Resaj/pumatron-v1/images/V1.2/DSCF2929.jpg

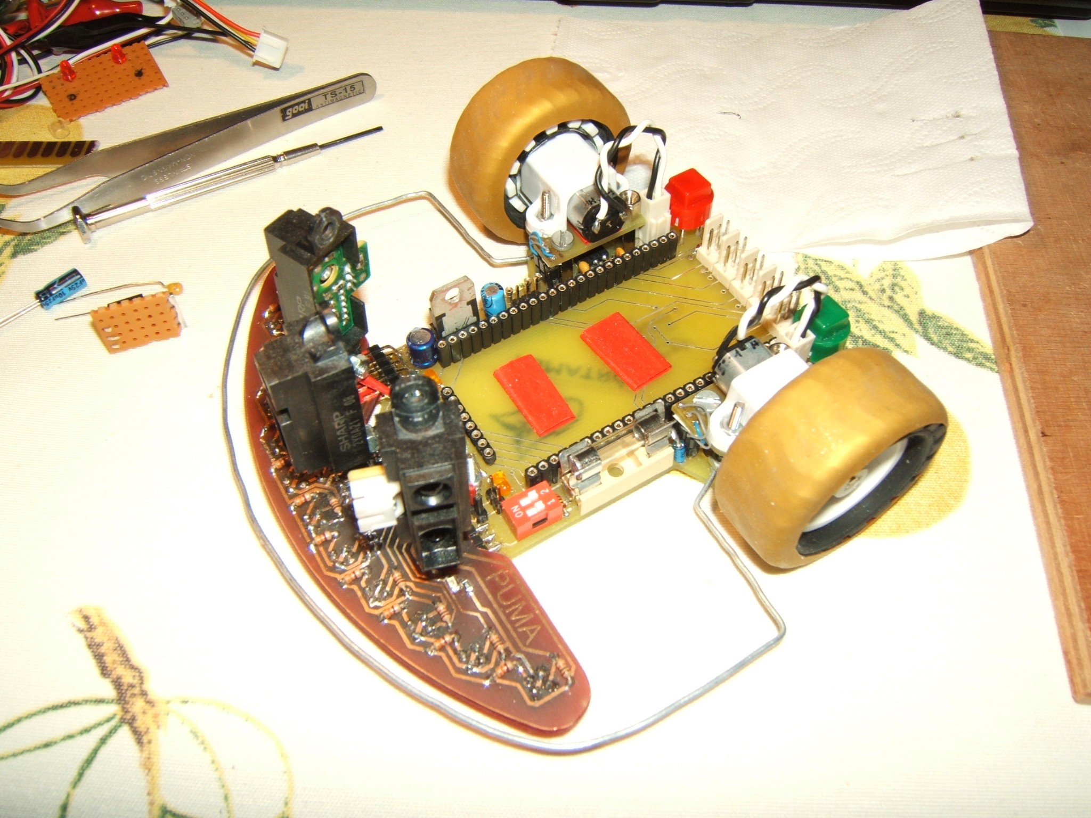
images/V1.2/DSCF2929.jpg
