Resaj/pumatron-v1/images/V1.2/Foto0010.jpg

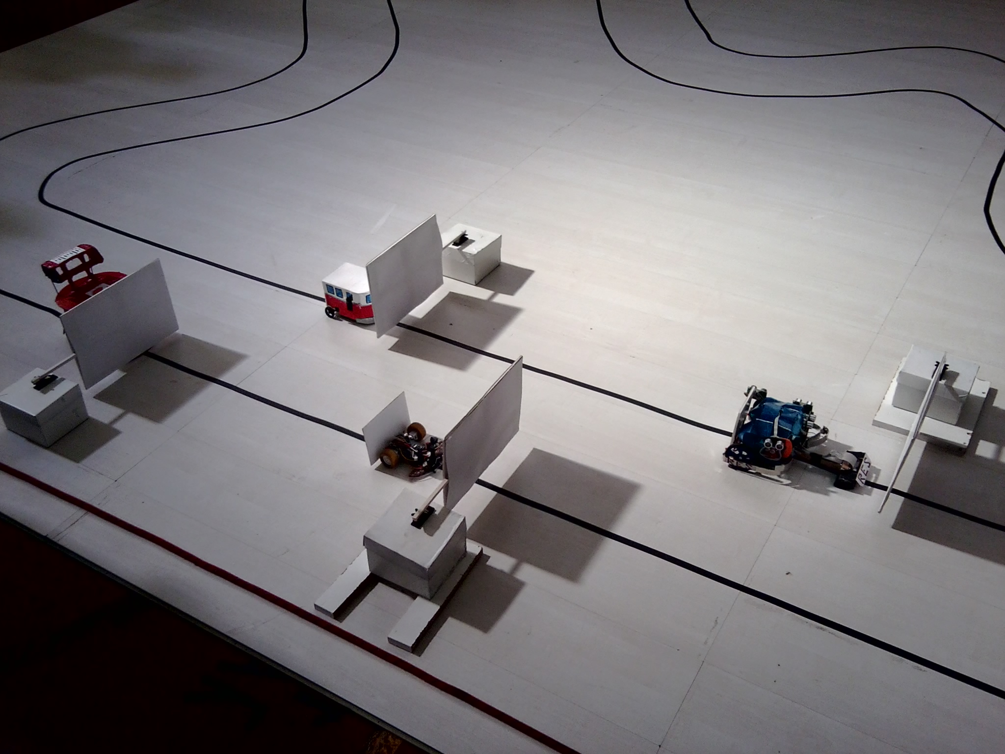
images/V1.2/Foto0010.jpg
