Resaj/pumatron-v1/Pumatron V1.2/Rastreador/Programa rastreador V1.2.2 Robolid 2012/Control.c

#include <lpc213x.h>
#include <stdlib.h>
#include <stdio.h>
#include "Declaraciones.h"
#include "s1d15g00.h"

/********************** FUNCIONES DE CONTROL **********************/
void selec_velocidad(void)
{
	if((IO0PIN&(1<<3)) == 0 && flag == 1)
	{
		if(v_rapida == (float)0.4)
		{
			IO0PIN &= ~((1<<27)|(1<<31));
			IO1PIN |= (1<<22)|(1<<23);
			v_rapida = 0.5;
		}
		else if(v_rapida == (float)0.5)
		{
			IO0PIN &= ~(1<<27);
			IO1PIN |= 1<<23;
			IO1PIN &= ~(1<<22);
			IO0PIN |= 1<<31;
			v_rapida = 0.6;
		}
		else if(v_rapida == (float)0.6)
		{
			IO0PIN &= ~(1<<27);
			IO1PIN |= (1<<22)|(1<<23);
			IO0PIN |= 1<<31;
			v_rapida = 0.7;
		}
		else if(v_rapida == (float)0.7)
		{
			IO0PIN |= 1<<27;
			IO1PIN &= ~((1<<22)|(1<<23));
			IO0PIN &= ~(1<<31);
			v_rapida = 0.8;
		}
		else if(v_rapida == (float)0.8)
		{
			IO0PIN |= 1<<27;
			IO1PIN &= ~(1<<23);
			IO1PIN |= 1<<22;
			IO0PIN &= ~(1<<31);
			v_rapida = 0.9;
		}
		else if(v_rapida == (float)0.9)
		{
			IO0PIN |= (1<<27)|(1<<31);
			IO1PIN &= ~(1<<22)|(1<<23);
			v_rapida = 1;
		}
		else // if(v_rapida == 1)
		{
			IO0PIN &= ~((1<<27)|(1<<31));
			IO1PIN |= (1<<23);
			IO1PIN &= ~(1<<22);
			v_rapida = 0.4;
		}
	}
	flag = (IO0PIN&(1<<3))>>3;

	for(t=0; t<100000; t++);	// Anti-rebotes
}

void leer_sensores(void)
{
	for(i=0; i<2; i++)
	{
		for(t=0; t<8; t++)
		{
			if(t != 0 && t != 4)
			{
				AD0CR |= (1<<24)|(1<<t);		/* Start A/D Conversion        */
				while ((AD0DR&(1<<31))==0);		/* Wait for end of A/D Convers.*/
				AD0CR &= ~((1<<24)|(1<<t));		/* Stop A/D Conversion         */
				ADC[t] = (AD0DR>>6)&0x03FC;		/* result of A/D process       */ 
			}
		}

		reordenar();
		conmutar_mux();
	}
}

void reordenar(void)
{
	if(mux == '0')
	{
		ADCresult[4] = ADC[1];
		ADCresult[2] = ADC[2];
		ADCresult[0] = ADC[3];
		ADCresult[6] = ADC[5];
		ADCresult[8] = ADC[6];
		ADCresult[10] = ADC[7];
	}
	else
	{
		ADCresult[5] = ADC[1];
		ADCresult[3] = ADC[2];
		ADCresult[1] = ADC[3];
		ADCresult[7] = ADC[5];
		ADCresult[9] = ADC[6];
		ADCresult[11] = ADC[7];
	}
}

void calibrar_sensores(void)
{
	for(i=0; i<S; i++)
	{
		if(ADCresult[i] < blanco[i])
		{
			blanco[i] = ADCresult[i];
			umbral[i] = (negro[i]+blanco[i])/2;
		}
		if(ADCresult[i] > negro[i])
		{
			negro[i] = ADCresult[i];
			umbral[i] = (negro[i]+blanco[i])/2;
		}
	}
}

void estimar_umbrales(void)
{
	cont = 0;

	for(i=0; i<S; i++)
	{
		if(ADCresult[i] < blanco[i])
			blanco[i] = ADCresult[i];
		if(ADCresult[i] > negro[i])
			negro[i] = ADCresult[i];

		if((negro[i]-blanco[i]) > 200)
		{
			cont++;
			umbral[i] = (negro[i]+blanco[i])/2;
		}
	}

	if(cont == S)
	{
		IO1PIN &= ~(1<<22);
		IO0PIN |= 1<<31;
	}

///**************** 1er algoritmo: valores aproximados suponiendo máximo 2 en negro ****************/
//	for(i=0; i<S; i++)
//	{
//		if(i == S/2-1 || i == S/2)
//		{
//			negro[i] = ADCresult[i];
//			blanco[i] = 0;
//		}
//		else
//		{
//			blanco[i] = ADCresult[i];
//			negro[i] = 1024;
//		}
//	}
//
//	inf = 0;
//	sup = 1023;
//	for(i=0; i<S; i++)
//	{
//		if(blanco[i] > inf)
//			inf = blanco[i];
//		if(negro[i] < sup)
//			sup = negro[i];
//	}
//
//	for(i=0; i<S; i++)
//	{
//		if(blanco[i] == 0)
//			blanco[i] = inf;
//		if(negro[i] == 1024)
//			negro[i] = sup;
//
//		umbral[i] = (negro[i]+blanco[i])/2;
//	}
//
///**************** 2do algoritmo: valores estimados ****************/
//	for(i=0; i<S; i++)
//	{
//		inf = ADCresult[i];
//		sup = ADCresult[i];
//
//		for(t=0; t<S; t++)
//		{
//			if(t != i)
//			{
//				if(ADCresult[t] < inf)
//					inf = ADCresult[t];
//				else if(ADCresult[t] > sup)
//					sup = ADCresult[t];
//			}
//		}
//
//		if((sup-ADCresult[i] < ADCresult[i]-inf) && (sup-ADCresult[i] < 100))
//		{
//			negro[i] = ADCresult[i];
//			blanco[i] = 0;
//		}
//		else if(sup-ADCresult[i] > ADCresult[i]-inf)
//		{
//			blanco[i] = ADCresult[i];
//			negro[i] = 1024;
//		}
//		else
//		{
//			blanco[i] = 0;
//			negro[i] = 1024;
//		}
//	}
//
//	inf = 0;
//	sup = 1023;
//	for(i=0; i<S; i++)
//	{
//		if(blanco[i] > inf)
//			inf = blanco[i];
//		if(negro[i] < sup)
//			sup = negro[i];
//	}
//
//	for(i=0; i<S; i++)
//	{
//		if(blanco[i] == 0)
//			blanco[i] = inf;
//		if(negro[i] == 1024)
//			negro[i] = sup;
//
//		umbral[i] = (negro[i]+blanco[i])/2;
//	}
//
///**************** 3er algoritmo: Valores por defecto ****************/
//	blanco[0] = 600;	negro[0] = 900;
//	blanco[1] = 600;	negro[1] = 900;
//	blanco[2] = 600;	negro[2] = 900;
//	blanco[3] = 600;	negro[3] = 900;
//	blanco[4] = 600;	negro[4] = 900;
//	blanco[5] = 600;	negro[5] = 900;
//	blanco[6] = 600;	negro[6] = 900;
//	blanco[7] = 600;	negro[7] = 900;
//	blanco[8] = 600;	negro[8] = 900;
//	blanco[9] = 600;	negro[9] = 900;
//	blanco[10] = 600;	negro[10] = 900;
//	blanco[11] = 600;	negro[11] = 900;
//
//	for(i=0; i<S; i++)
//		umbral[i] = (negro[i]+blanco[i])/2;


//	for(i = 0; i < S; i++)
//	{
//		sprintf(cadena, "[%d]", i);   
//		LCDPutStr(cadena, (120-(i*10)), 0, SMALL, WHITE, BLACK);
//		sprintf(cadena, "%4u  %4u", blanco[i], negro[i]);   
//		LCDPutStr(cadena, (120-(i*10)), 25, SMALL, WHITE, BLACK);
//	}
//	sprintf(cadena, "inf");   
//	LCDPutStr(cadena, 90, 100, SMALL, WHITE, BLACK);
//	sprintf(cadena, "%d", inf);   
//	LCDPutStr(cadena, 75, 100, SMALL, WHITE, BLACK);
//	sprintf(cadena, "sup");   
//	LCDPutStr(cadena, 50, 100, SMALL, WHITE, BLACK);
//	sprintf(cadena, "%d", sup);   
//	LCDPutStr(cadena, 35, 100, SMALL, WHITE, BLACK);
}

void digitalizar(void)
{
	for(i=0; i<S; i++)
	{
		if(ADCresult[i] > umbral[i])
			LINEAresult[i] = 1;
		else
			LINEAresult[i] = 0;
	}
}

void detectar_secuencias(void)
{
	// Número de sensores en negro
	for (i=0; i<S; i++)
		negros += LINEAresult[i];

	// Si detectamos 101 hay hueco y consideramos sólo 2 sensores juntos
	for (i=0; i<S; i++)
	{
		if (LINEAresult[i] == 1 && marca[0] == false)
		{
			aux_act[0] = i;
			marca[0] = true;
		}
		else if (LINEAresult[i] == 0 && marca[0] == true && marca[1] == false)
			marca[1] = true;
		else if (LINEAresult[i] == 1 && marca[1] == true && marca[2] == false)
		{
			aux_act[1] = i;
			marca[2] = true;
			secuencia_actual = '2';
		}
		else if (LINEAresult[i] == 0 && marca[2] == true && marca[3] == false)
			marca[3] = true;
		else if (LINEAresult[i] == 1 && marca[3] == true)
		{
			secuencia_actual = '3';
			if(cond == '1')
				cond = '0';
		} 
	}

	for (i=S-1; i>-1; i--)
	{
		if (LINEAresult[i] == 1 && marca[4] == false)
		{
			aux_act[2] = i;
			marca[4] = true;
		}
		else if (LINEAresult[i] == 0 && marca[4] == true && marca[5] == false)
			marca[5] = true;
		else if (LINEAresult[i] == 1 && marca[5] == true && marca[6] == false)
		{
			aux_act[3] = i;
			marca[6] = true;
		}
	}

	// Si hay más de 2 sensores en negro y no hay huecos, tenemos más de 2 sensores juntos en negro
	if (secuencia_actual == '1' && negros > 2)
		secuencia_actual = '7';

	// Evitar tomar el camino malo en la bifurcación si por inercia se ha pasado el bueno
	if(ESTADO == Bifurcacion && GIRO != REC)
	{
		if(GIRO == DER)
		{
			if((aux_act[0] > aux_ant[0] + 1) && (aux_ant[0] <= 1))
			{
				for(i=aux_act[0]; i<aux_act[2]+1; i++)
					LINEAresult[i] = 0;
				aux_act[0] = aux_ant[0];

				giro = DER;
				linea_buena = false;
				negros = 0;
			}
			else
				linea_buena = true;
		}
		else	// GIRO == IZQ
		{
			if((aux_act[2] < aux_ant[2] - 1) && (aux_ant[2] >= S-2))
			{
				for(i=aux_act[0]; i<aux_act[2]+1; i++)
					LINEAresult[i] = 0;
				aux_act[2] = aux_ant[2];

				giro = IZQ;
				linea_buena = false;
				negros = 0;
			}
			else
				linea_buena = true;
		}
	}
}

void borrar_marca(void)
{
	if(aux_ant[0] > aux_act[0] + 1)	// Los negros detectados en los instantes actual y anterior por la derecha están separados
		GIRO_aux_der = '1';
	else if(aux_ant[0] < aux_act[0] - 1)
		GIRO_aux_der = '0';
	if(aux_ant[2] < aux_act[2] - 1)	// Los negros detectados en los instantes actual y anterior por la izquierda están separados
		GIRO_aux_izq = '1';
	else if(aux_ant[2] > aux_act[2] + 1)
		GIRO_aux_izq = '0';

	// Borrar marca de giro
	if(GIRO_aux_der == '1')
	{
		for(i=aux_act[1]-2; i>=aux_act[0]; i--)
			LINEAresult[i] = 0;
		aux_act[0] = aux_act[1];
	}
	if(GIRO_aux_izq == '1')
	{
		for(i=aux_act[3]+2; i<=aux_act[2]; i++)
			LINEAresult[i] = 0;
		aux_act[2] = aux_act[3];
	}
}

void borrar_linea(void)
{
	if(GIRO == DER) // Estamos en un cruce y debemos girar a la derecha
	{
		for(i=aux_act[0]+2; i<S; i++)
			LINEAresult[i] = 0;
		giro = IZQ;	// Evitar que se pierda la línea si es giro cerrado a izquierda y no bifurcación
	}
	else if(GIRO == IZQ) // Estamos en un cruce y debemos girar a la izquierda
	{
		for(i=aux_act[2]-2; i>-1; i--)
			LINEAresult[i] = 0;
		giro = DER;	// Evitar que se pierda la línea si es giro cerrado a derecha y no bifurcación
	}
	else if(GIRO == REC && secuencia_actual != '7')	// GIRO == REC y hay más de una línea
	{
		if(abs((float)aux_act[1] - (S-1)/2) < abs((float)aux_act[0] - (S-1)/2))	// aux_act[1] está más cerca del centro que aux_act[0]
		{
			for(i=aux_act[1]-2; i>-1; i--)
				LINEAresult[i] = 0;
			for(i=aux_act[1]+2; i<S; i++)
				LINEAresult[i] = 0;
			giro = DER;	// Evitar que se pierda la línea si es giro cerrado a izquierda y no bifurcación
						// Se establece a derechas porque es la única bifurcación que sabemos que existe
		}
		else	// aux_act[0] está más cerca del centro que aux_act[1]
		{
			// Se borra sólo el lado izquierdo porque en el derecho no hay línea
			for(i=aux_act[0]+2; i<S; i++)
				LINEAresult[i] = 0;
			giro = IZQ;	// Evitar que se pierda la línea si es giro cerrado a izquierda y no bifurcación
		}
	}
}

void actualizar(void)
{
	// Variables para la detección de secuencia
	for(i=0; i<7; i++)
		marca[i] = 0;

	negros = 0;
	cond = '1';

	secuencia_anterior = secuencia_actual;
	secuencia_actual = '1';

	// Variables para la detección de la marca de giro
	for(i=0; i<4; i++)
		aux_ant[i] = aux_act[i];
	aux_act[0] = 16;		// Se iguala a un número mayor que el número de sensores para evitar errores en estados siguientes
	aux_act[2] = -2;		// Se iguala a un número menor que -1 para evitar errores en estados siguientes

	// Visualización de los datos
	if(GIRO == REC)
	{
		IO0PIN |= 1<<27;
		IO1PIN |= 1<<23;
	}
	else if(GIRO == IZQ)
	{
		IO0PIN &= ~(1<<27);
		IO1PIN |= 1<<23;
	}
	else if(GIRO == DER)
	{
		IO0PIN |= 1<<27;
		IO1PIN &= ~(1<<23);
	}
	
	if(giro == IZQ)
	{
		IO0PIN &= ~(1<<31);
		IO1PIN |= 1<<22;
	}
	else if(giro == DER)
	{
		IO0PIN |= 1<<31;
		IO1PIN &= ~(1<<22);
	}
}

void conmutar_mux(void)
{
	// Conmutar sensores
	if(mux == '0')
	{
		mux = '1';
		IO0PIN |= (1<<25);
	}
	else
	{
		mux = '0';
		IO0PIN &= ~(1<<25);
	}
}
