Resaj/pumatron-v1/Pumatron V1.2/Rastreador/Programa rastreador V1.2.1 Alcabot 2012/PID.h

#ifndef PID_h
#define PID_h

//Variables PID
extern int sensors_average;
extern int sensors_sum;
extern int position;
extern int proportional;
extern long integral;
extern long integral_max;
extern int derivative;
extern int last_proportional;
extern int control_value;
extern int max_difference;
extern float Kp;
extern float Ki;
extern float Kd;

#endif


// Funciones de control
void get_PID(void);
void set_motors(void);
void loop_PID(void);
